jywilson2/charuco/stl/bambu_labs_x1e/part_4_white.stl

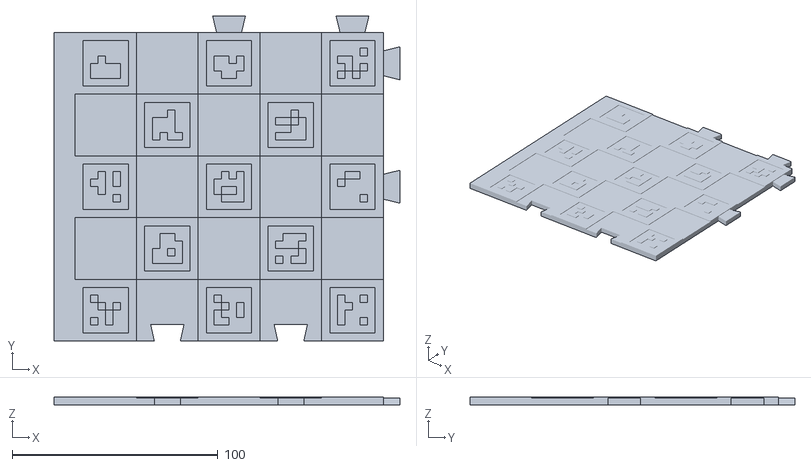
[picture p18: CAD file, 2026-02-05]
stl/bambu_labs_x1e/part_4_white.stl
168.0 x 158.0 x 4.00
