jywilson2/charuco/stl/prusa_xl/part2_white.stl

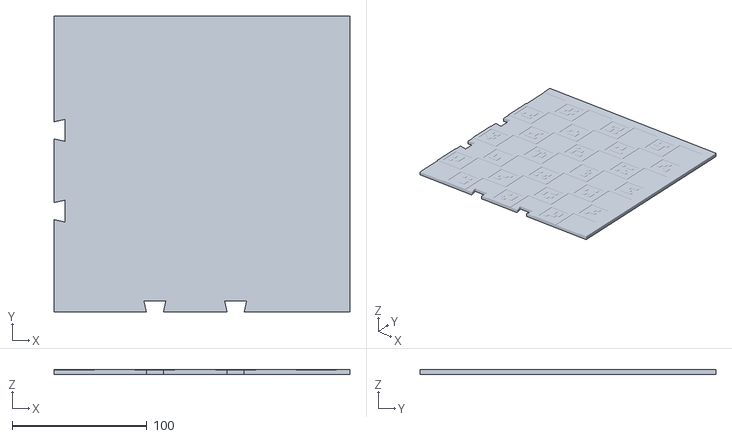
[picture p19: CAD file, 2026-02-05]
stl/prusa_xl/part2_white.stl
220.0 x 220.0 x 4.00
