jywilson2/charuco/stl/bambu_labs_x1e/part_5_black.stl

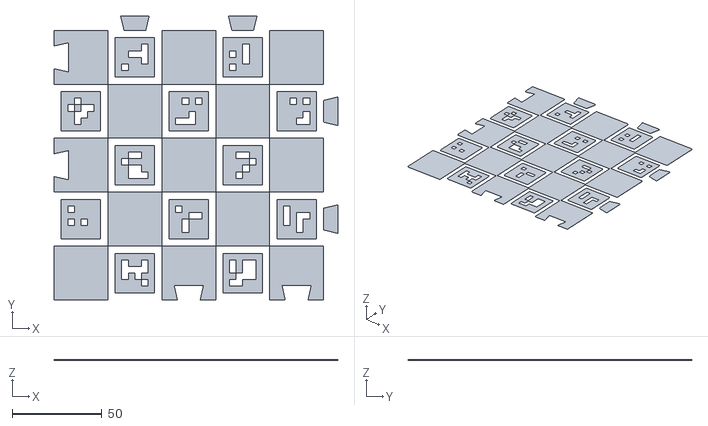
[picture p20: CAD file, 2026-02-05]
stl/bambu_labs_x1e/part_5_black.stl
158.0 x 158.0 x 0.6
