jywilson2/charuco/stl/bambu_labs_x1e/part_9_white.stl

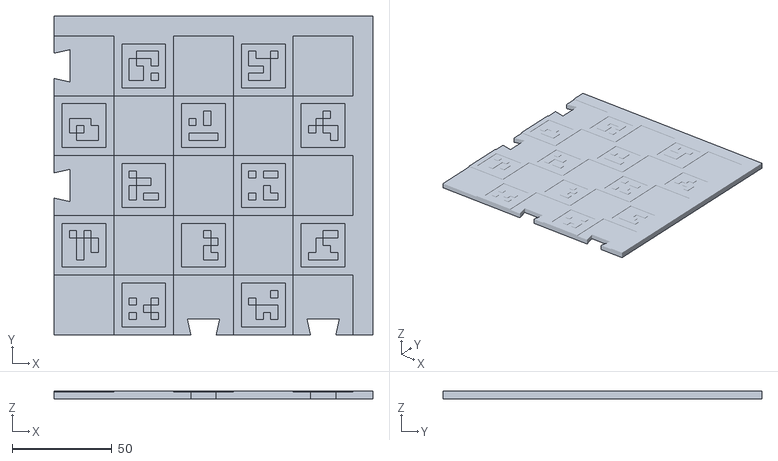
[picture p21: CAD file, 2026-02-05]
stl/bambu_labs_x1e/part_9_white.stl
160.0 x 160.0 x 4.00
