jywilson2/charuco/stl/bambu_labs_x1e/part_1_white.stl

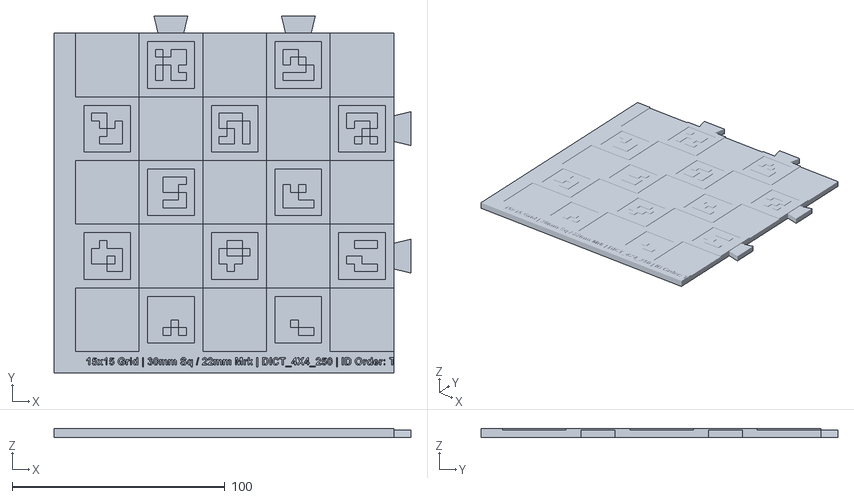
[picture p22: CAD file, 2026-02-05]
stl/bambu_labs_x1e/part_1_white.stl
168.0 x 168.0 x 4.00
