jywilson2/charuco/stl/bambu_labs_x1e/part_5_white.stl

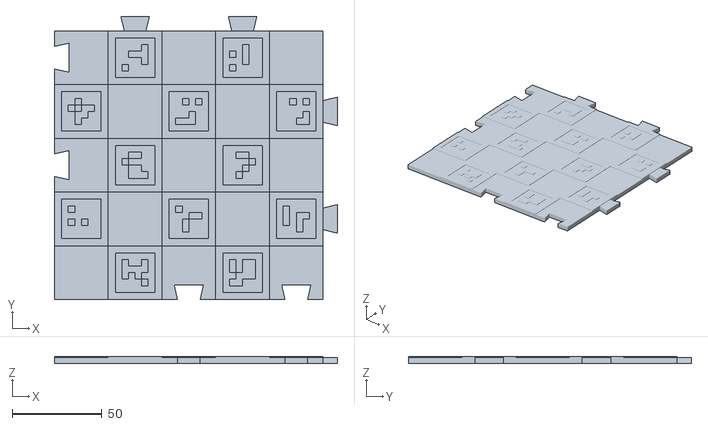
[picture p23: CAD file, 2026-02-05]
stl/bambu_labs_x1e/part_5_white.stl
158.0 x 158.0 x 4.00
