jywilson2/charuco/stl/bambu_labs_x1e/part_9_black.stl

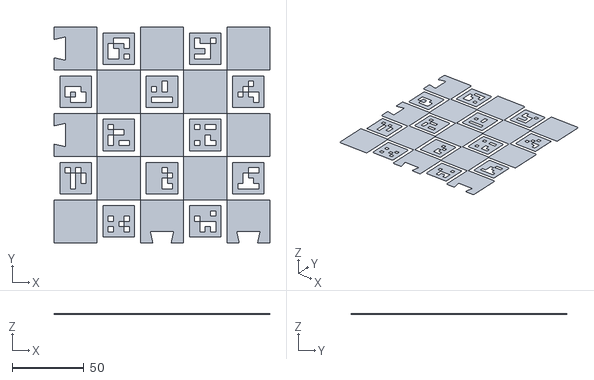
[picture p24: CAD file, 2026-02-05]
stl/bambu_labs_x1e/part_9_black.stl
150.0 x 150.0 x 0.6
